sparkfun/SparkFun_MicroMod_LTE_GNSS_Function_Board_u-blox_SARA-R5/docs/assets/img/Example3_Network_Profile_error.JPG

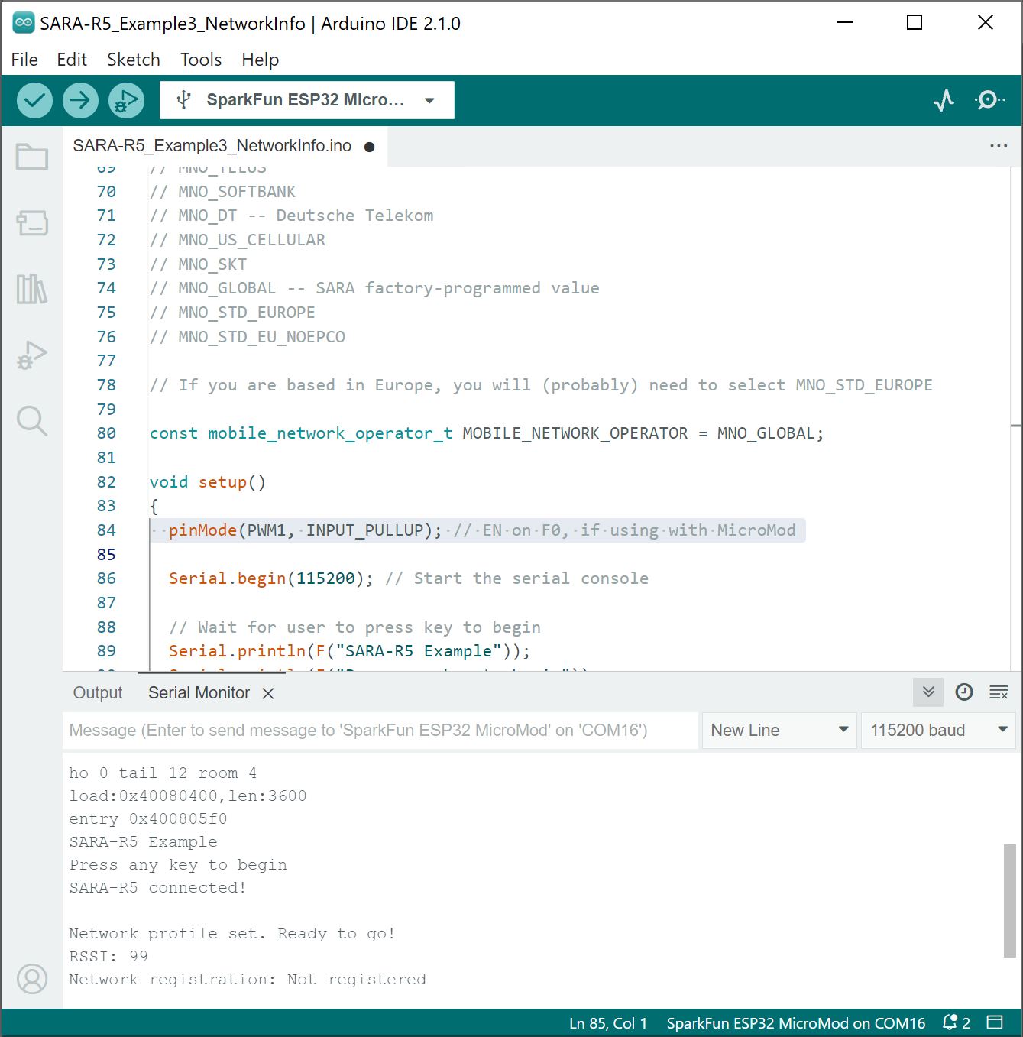
docs/assets/img/Example3_Network_Profile_error.JPG
