sparkfun/SparkFun_MicroMod_LTE_GNSS_Function_Board_u-blox_SARA-R5/docs/assets/img/Example4_RegisterOperator_Wait_NI.JPG

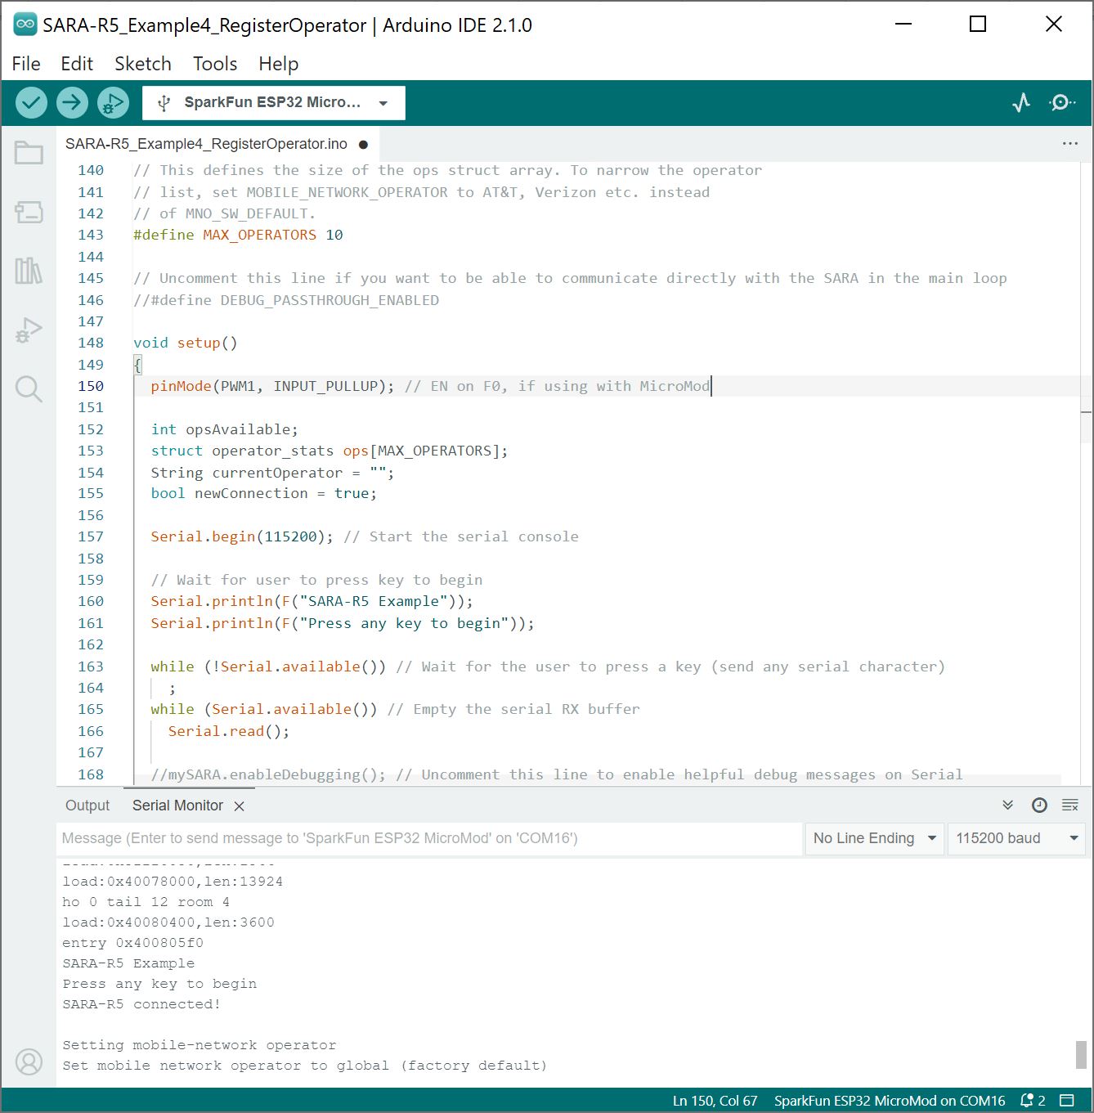
docs/assets/img/Example4_RegisterOperator_Wait_NI.JPG
